StonedEdge/WiiSPii/src/PICCONFIG.h

#ifndef PICCONFIG_H
#define	PICCONFIG_H

// PIC16F15324 Configuration Bit Settings

#define _XTAL_FREQ 32000000
#define TMR1_RST    65228

// CONFIG1
#pragma config FEXTOSC = OFF    // External Oscillator mode selection bits (Oscillator not enabled)
#pragma config RSTOSC = HFINT32 // Power-up default value for COSC bits (HFINTOSC with OSCFRQ= 32 MHz and CDIV = 1:1)
#pragma config CLKOUTEN = OFF   // Clock Out Enable bit (CLKOUT function is disabled; i/o or oscillator function on OSC2)
#pragma config CSWEN = ON       // Clock Switch Enable bit (Writing to NOSC and NDIV is allowed)
#pragma config FCMEN = ON       // Fail-Safe Clock Monitor Enable bit (FSCM timer enabled)

// CONFIG2
#pragma config MCLRE = OFF      // Master Clear Enable bit (MCLR pin function is port defined function)
#pragma config PWRTE = OFF      // Power-up Timer Enable bit (PWRT disabled)
#pragma config LPBOREN = OFF    // Low-Power BOR enable bit (ULPBOR disabled)
#pragma config BOREN = ON       // Brown-out reset enable bits (Brown-out Reset Enabled, SBOREN bit is ignored)
#pragma config BORV = LO        // Brown-out Reset Voltage Selection (Brown-out Reset Voltage (VBOR) set to 1.9V on LF, and 2.45V on F Devices)
#pragma config ZCD = OFF        // Zero-cross detect disable (Zero-cross detect circuit is disabled at POR.)
#pragma config PPS1WAY = OFF    // Peripheral Pin Select one-way control (The PPSLOCK bit can be set and cleared repeatedly by software)
#pragma config STVREN = ON      // Stack Overflow/Underflow Reset Enable bit (Stack Overflow or Underflow will cause a reset)

// CONFIG3
#pragma config WDTCPS = WDTCPS_13// WDT Period Select bits (Divider ratio 1:262144)
#pragma config WDTE = ON        // WDT operating mode (WDT enabled regardless of sleep; SWDTEN ignored)
#pragma config WDTCWS = WDTCWS_7// WDT Window Select bits (window always open (100%); software control; keyed access not required)
//#pragma config WDTCCS = HFINTOSC// WDT input clock selector (WDT reference clock is the 31.25 kHz HFINTOSC)
#pragma config WDTCCS = LFINTOSC// WDT input clock selector (WDT reference clock is the 31.0kHz LFINTOSC output)

// CONFIG4
#pragma config BBSIZE = BB512   // Boot Block Size Selection bits (512 words boot block size)
#pragma config BBEN = OFF       // Boot Block Enable bit (Boot Block disabled)
#pragma config SAFEN = OFF      // SAF Enable bit (SAF disabled)
#pragma config WRTAPP = OFF     // Application Block Write Protection bit (Application Block not write protected)
#pragma config WRTB = OFF       // Boot Block Write Protection bit (Boot Block not write protected)
#pragma config WRTC = OFF       // Configuration Register Write Protection bit (Configuration Register not write protected)
#pragma config WRTSAF = OFF     // Storage Area Flash Write Protection bit (SAF not write protected)
#pragma config LVP = OFF         // Low Voltage Programming Enable bit (Low Voltage programming enabled. MCLR/Vpp pin function is MCLR.)

// CONFIG5
#pragma config CP = OFF         // UserNVM Program memory code protection bit (UserNVM code protection disabled)

//Pin definitions
#define pwr_btn     RA5
#define enable      RC5
#define aux         RA2    
#define thermistor  RA4

//PWM 3 4 5 on RC2, RC3, RC4

#include <xc.h> // include processor files - each processor file is guarded.  

#endif	
