StonedEdge/WiiSPii/src/PPS.c

#include <xc.h>

void PPS_unlock() {
    PPSLOCK = 0x55;
    PPSLOCK = 0xAA;
    PPSLOCK = 0; //PPS unlocked	
}

void PPS_lock() {
    PPSLOCK = 0x55;
    PPSLOCK = 0xAA;
    PPSLOCK = 1; //PPS locked   	
}
